imaginaryimpedance/Differential-Probe/Simulations/AD8129 - Copy.asc

C1: cap; 2p
C2: cap; 2p
C9: cap; 2000p
C12: cap; 2000p
R1: res; 5Meg
R2: res; 5Meg
R3: res; 220k
R4: res; 100R
R5: res; 100R
R6: res; 50R
R7: res; 220k
R8: res; 143
R9: res; 5.1k
R10: res; 5.1k
R11: res; 576
R13: res; 10k
U1: AD8130
U2: THS3491RGT
V1: voltage; 0; AC 1000V
V2: voltage; 15V
V3: voltage; 15V
V4: voltage; -0.55V
Named nets: 0, VCC, VEE, OUTPUT
.ac dec 100 1k 100MEG
x1000 Attenuation
x2 Gain
x5 Gain
DC Offset Comp.
