imaginaryimpedance/Differential-Probe/Simulations/Input Protection.asc

C1: cap; 2p
C2: cap; 2p
C9: cap; 200p
C12: cap; 200p
D1: diode; 1N4148
D2: diode; 1N4148
D3: diode; 1N4148
D4: diode; 1N4148
R1: res; 5Meg
R2: res; 5Meg
R3: res; 220k
R4: res; 100R
R5: res; 100R
R6: res; 50R
R7: res; 220k
R8: res; 143
R9: res; 64k
R10: res; 64k
R11: res; 576
R12: res; 10k
R13: res; 10k
R14: res; 3.3k
R15: res; 10k
R16: res; 3.3k
U1: AD8130
U2: THS3491RGT
V1: voltage; PULSE(0 2000V 0 1 1 1 1)
V2: voltage; 12V
V3: voltage; 12V
V4: voltage; -0.55V
Named nets: 0, VCC, VEE, OUTPUT, Prot_P, Prot_N, IN_P, IN_N, ATT_N, ATT_P
.tran 1s
x1000 Attenuation
x2 Gain
x5 Gain
DC Offset Comp.
