imaginaryimpedance/Differential-Probe/Simulations/Comparator_output_delay.asc

C1: cap; 330n
M1: nmos; Si7336ADP
R1: res; 3.3Meg
R2: res; 10R
V1: voltage; 5V
V2: voltage; PULSE(0 5 1s 1n 1n 100ns)
Named nets: 0
.tran 10s
